czeppi/Black-Pearl/pics/keyboard-left-01.jpg

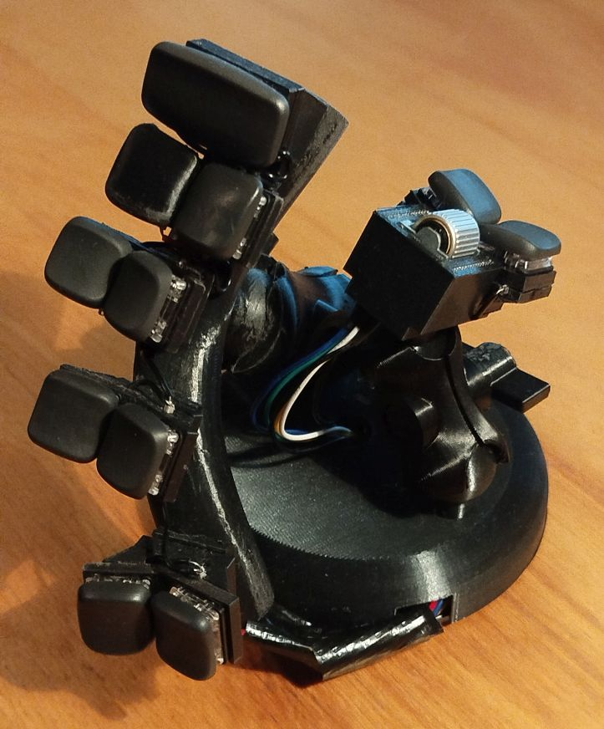
pics/keyboard-left-01.jpg
