czeppi/Black-Pearl/pics/keyboard-left-04.jpg

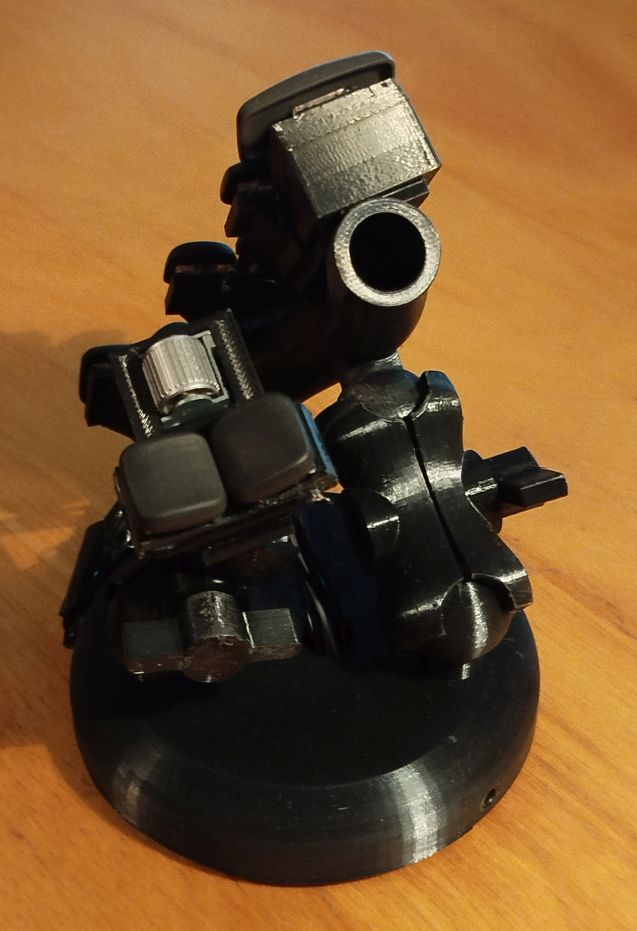
pics/keyboard-left-04.jpg
