czeppi/Black-Pearl/pics/keyboard-left-06.jpg

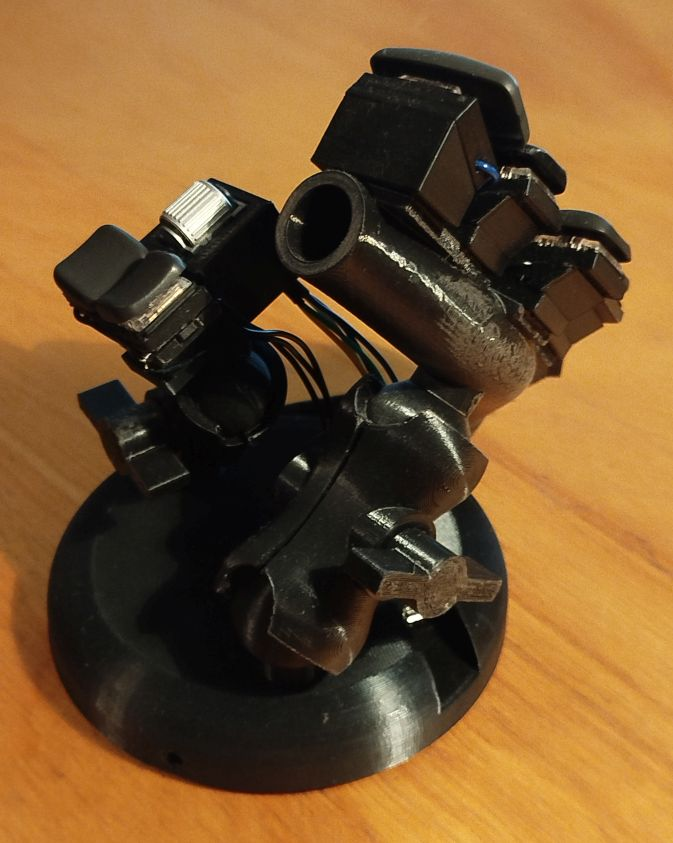
pics/keyboard-left-06.jpg
