czeppi/Black-Pearl/pics/keyboard-right-02.jpg

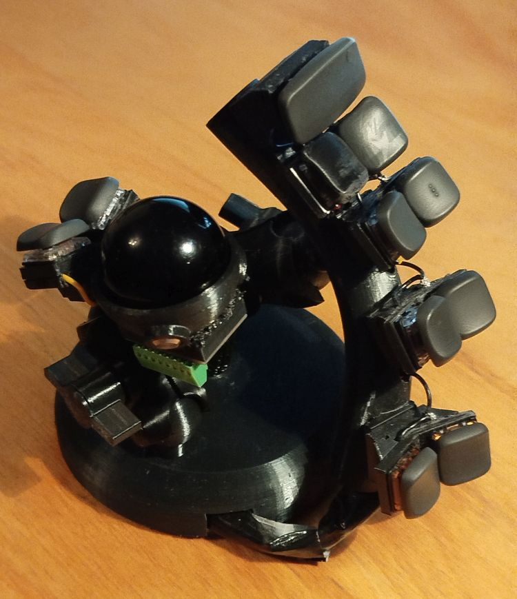
pics/keyboard-right-02.jpg
