czeppi/Black-Pearl/pics/keyboard-right-05.jpg

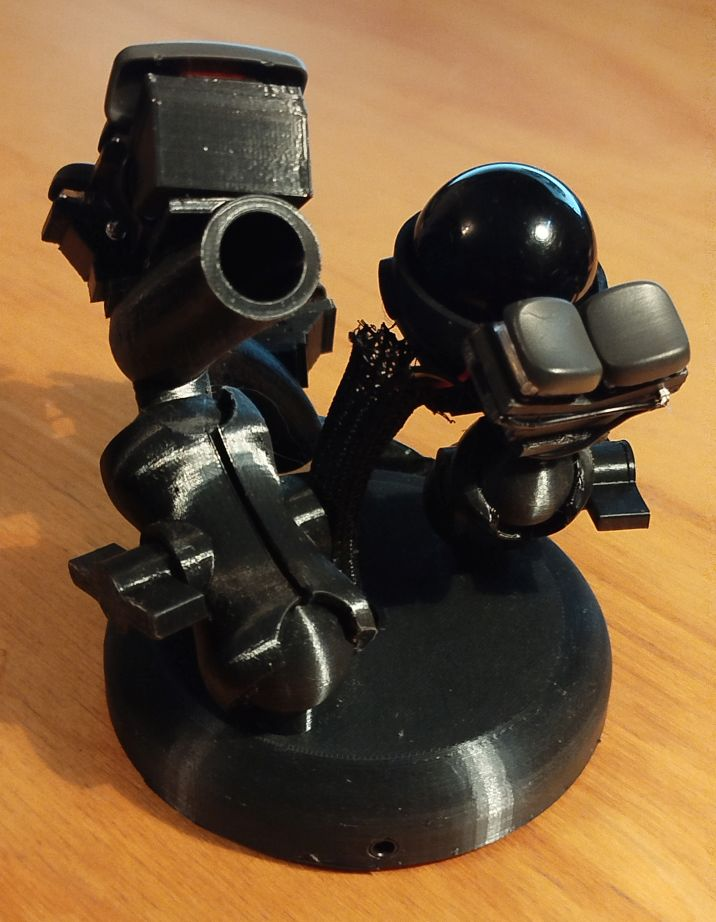
pics/keyboard-right-05.jpg
