czeppi/Black-Pearl/pics/keyboard-right-06.jpg

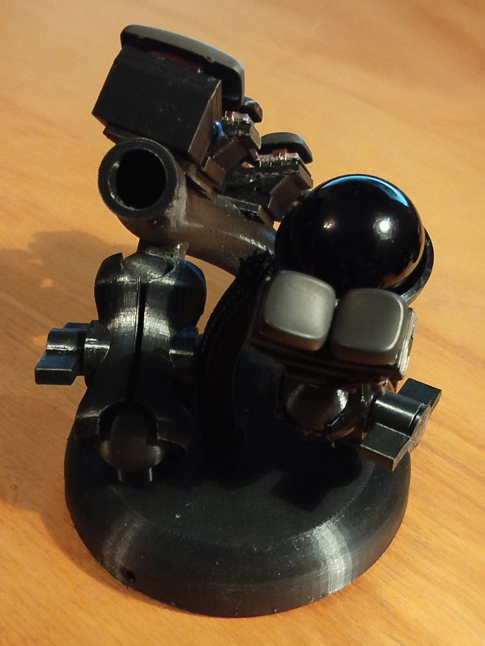
pics/keyboard-right-06.jpg
