czeppi/Black-Pearl/stl/case/single-switch-top.stl

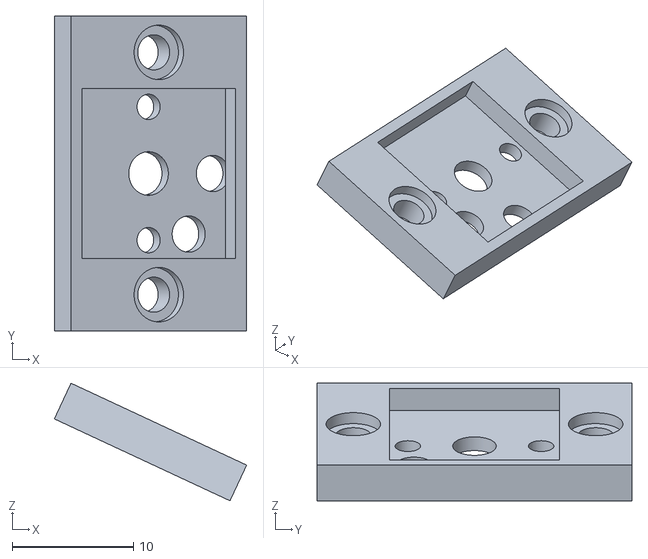
[picture p30: CAD file, 2026-03-14]
stl/case/single-switch-top.stl
15.9 x 26.0 x 9.71
