czeppi/Black-Pearl/stl/case/trrs_stopper.stl

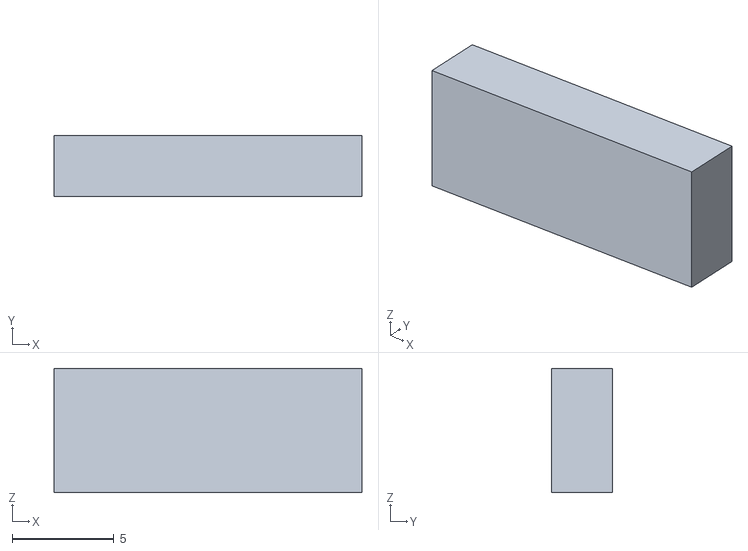
[picture p31: CAD file, 2026-03-14]
stl/case/trrs_stopper.stl
15.1 x 3.00 x 6.10
