czeppi/Black-Pearl/stl/case/single-switch-foot.stl

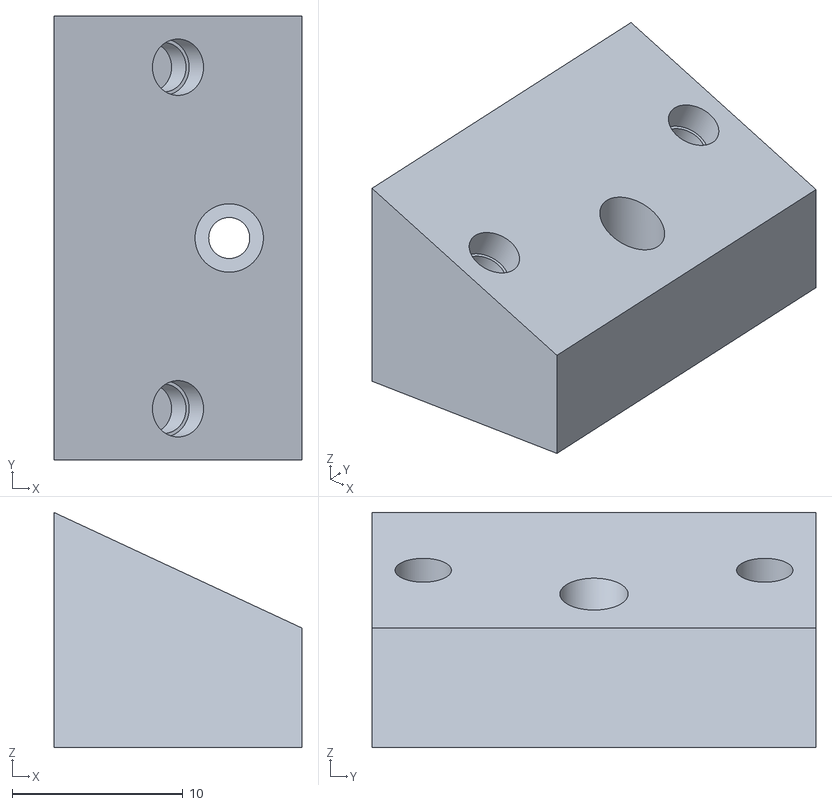
[picture p32: CAD file, 2026-03-14]
stl/case/single-switch-foot.stl
14.5 x 26.0 x 13.8
