czeppi/Black-Pearl/stl/case/trackball-holder.stl

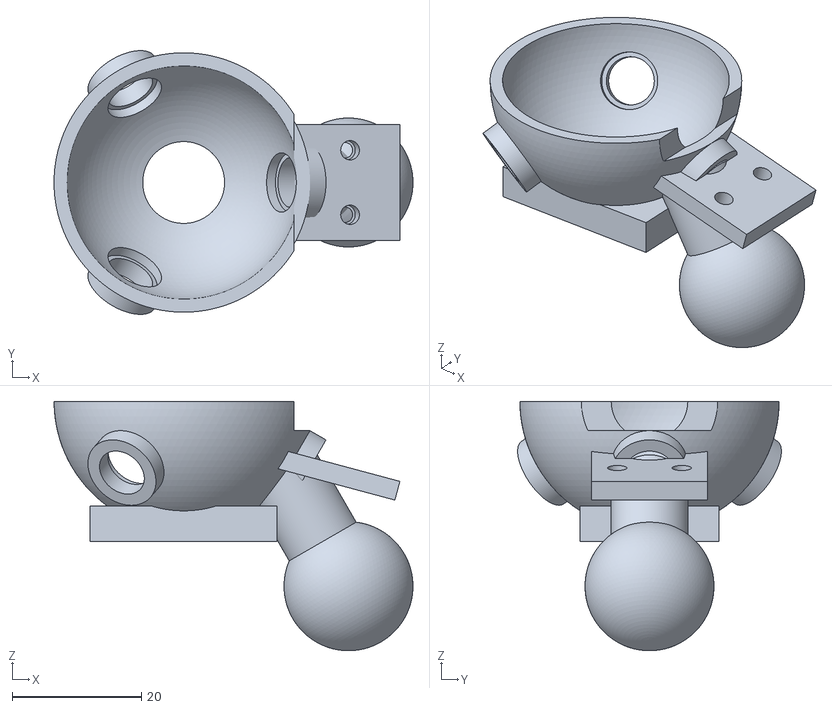
[picture p34: CAD file, 2026-03-13]
stl/case/trackball-holder.stl
55.6 x 40.9 x 38.7
