czeppi/Black-Pearl/stl/case/switch-pair-foot.stl

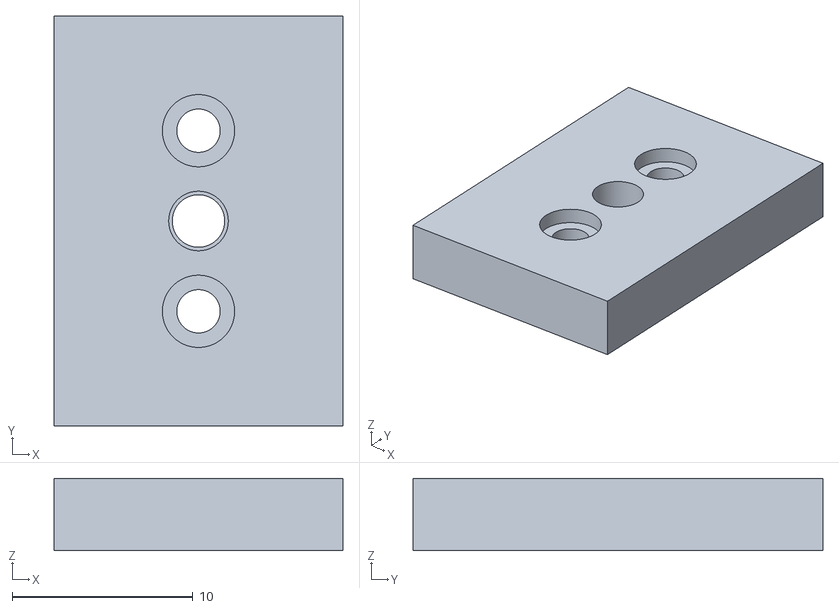
[picture p35: CAD file, 2026-03-13]
stl/case/switch-pair-foot.stl
16.0 x 22.7 x 4.00
