czeppi/Black-Pearl/stl/case/switch-pair-middle.stl

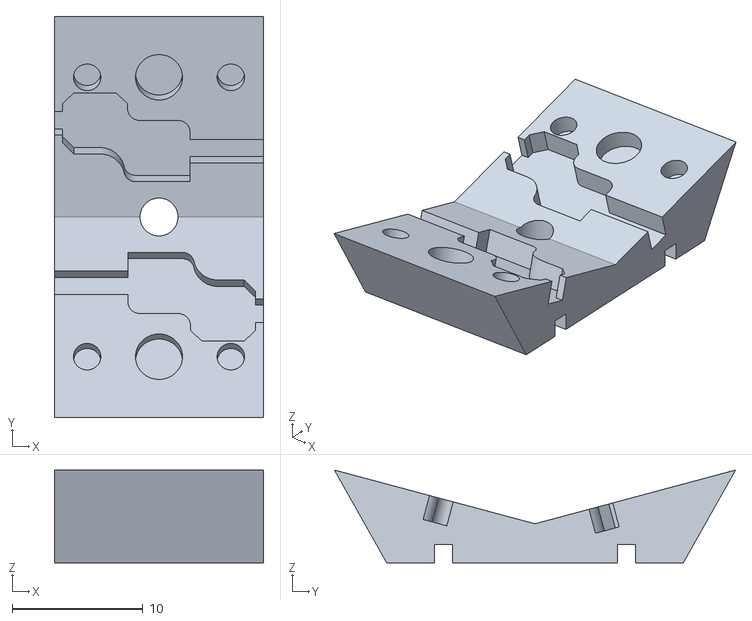
[picture p36: CAD file, 2026-03-13]
stl/case/switch-pair-middle.stl
16.0 x 30.7 x 7.12
