czeppi/Black-Pearl/stl/case/skeleton-with-sphere.stl

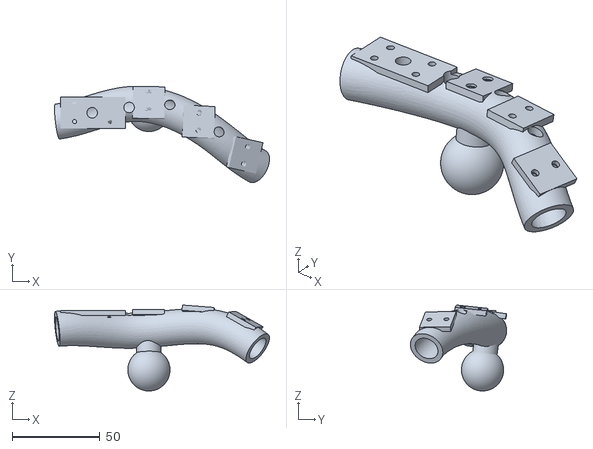
[picture p37: CAD file, 2026-03-13]
stl/case/skeleton-with-sphere.stl
122.2 x 54.8 x 48.9
