czeppi/Black-Pearl/stl/case/finger-double-ball-holder2.stl

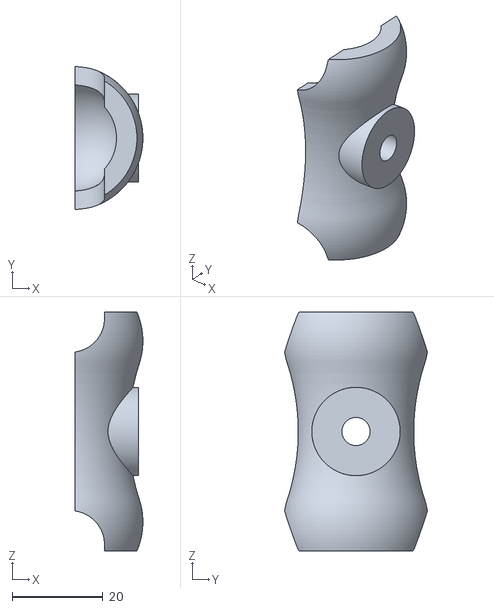
[picture p38: CAD file, 2026-03-13]
stl/case/finger-double-ball-holder2.stl
15.0 x 31.6 x 52.8
