czeppi/Black-Pearl/firmware/both_base.py

from __future__ import annotations

PhysicalKeySerial = int  # p.e. LEFT_PINKY_DOWN
VirtualKeySerial = int  # p.e. LPD
LayerID = int

TimeInMs = float
KeyCode = int  # 0 - 255
KeyName = str  # in layer description in both_kbdlayoutdata.py (must be unique)
